Camsu04/SMACAR-Project/Software/dashboard/DASHBOARD BLYNK.png

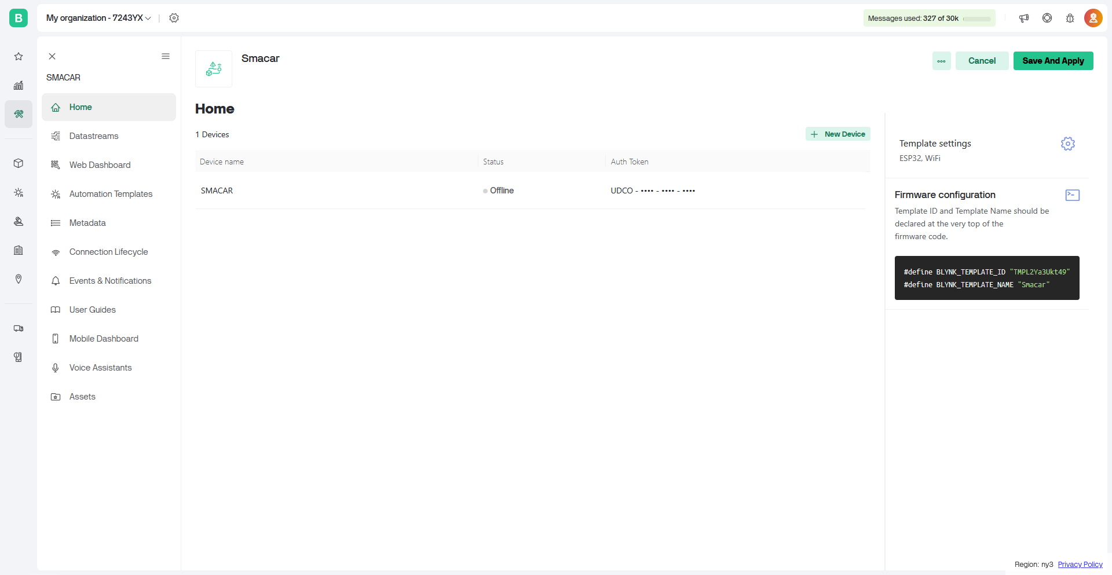
Software/dashboard/DASHBOARD BLYNK.png
