Camsu04/SMACAR-Project/Hardware/3D Design/Carcasa LoRaWAN/Parte Inferior V2.STL

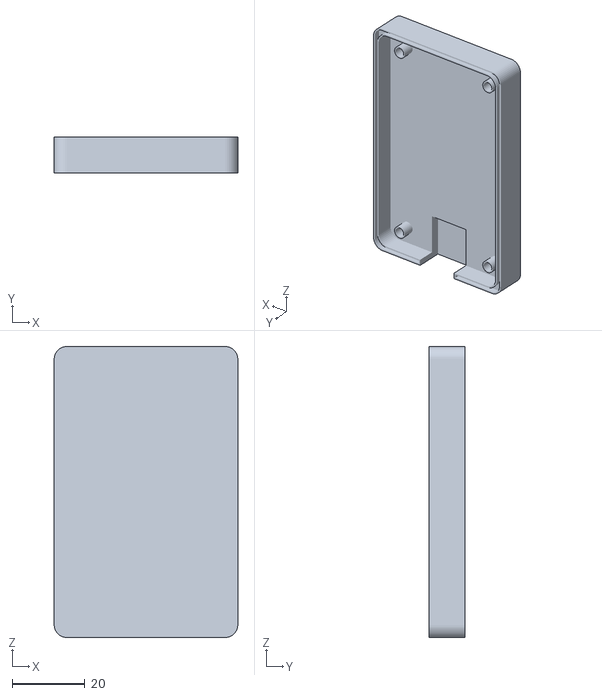
[picture p31: CAD file, 2025-08-08, an earlier design]
Hardware/3D Design/Carcasa LoRaWAN/Parte Inferior V2.STL
50.5 x 10.0 x 80.0
