Camsu04/SMACAR-Project/Hardware/3D Design/Carcasa LoRaWAN/Ensamble.SLDASM

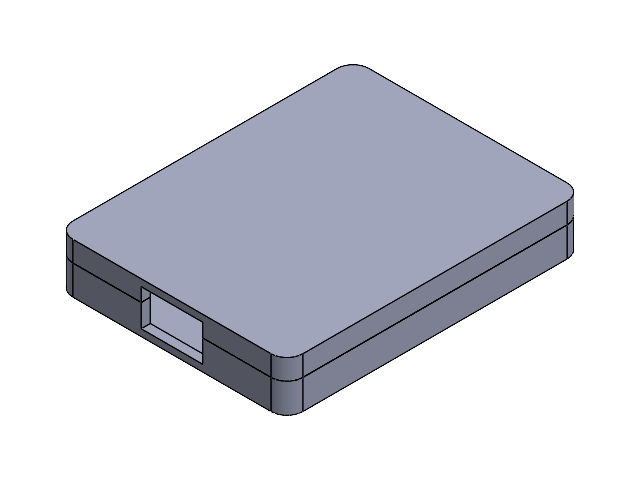
[picture p32: CAD file, 2025-08-06]
Hardware/3D Design/Carcasa LoRaWAN/Ensamble.SLDASM
Parte Inferior
Parte Superior
