Camsu04/SMACAR-Project/Documentacion/LoraWan Module/476259524eca3c4d4986ae6d08e4b8ac.pdf

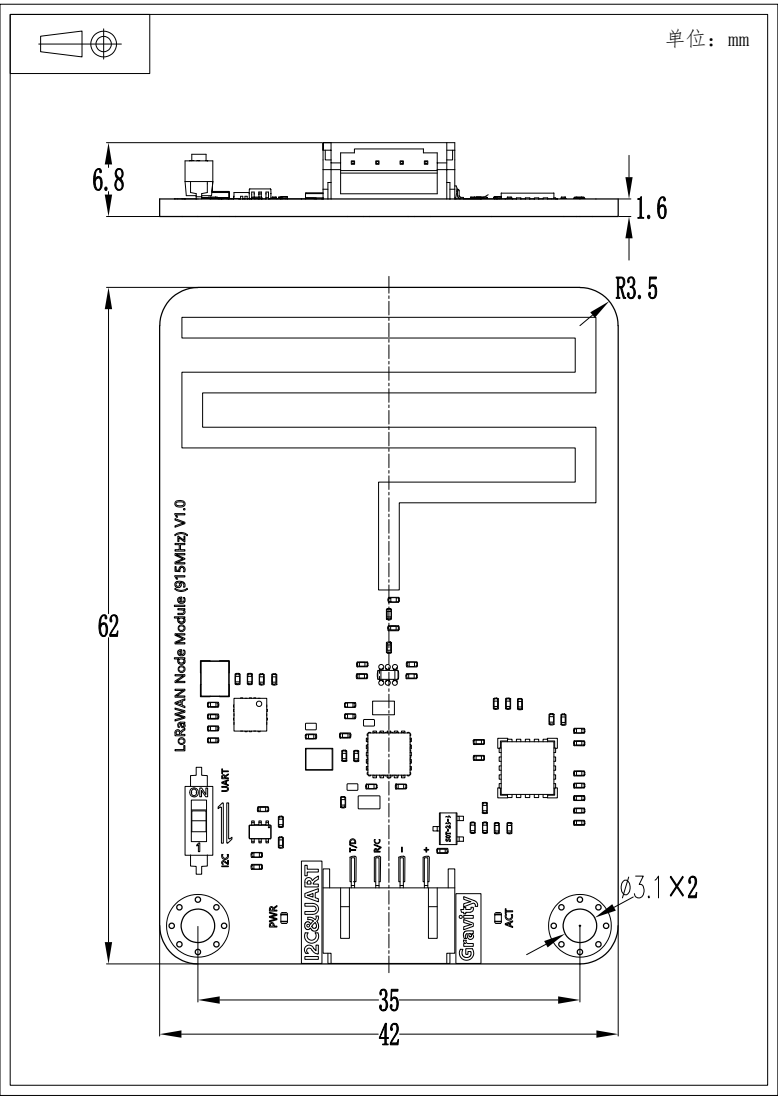
[picture p36: page 1]
